rseitz01/fhgr-bachelorthesis-camera-calibration/doc/pres/single-led.jpg

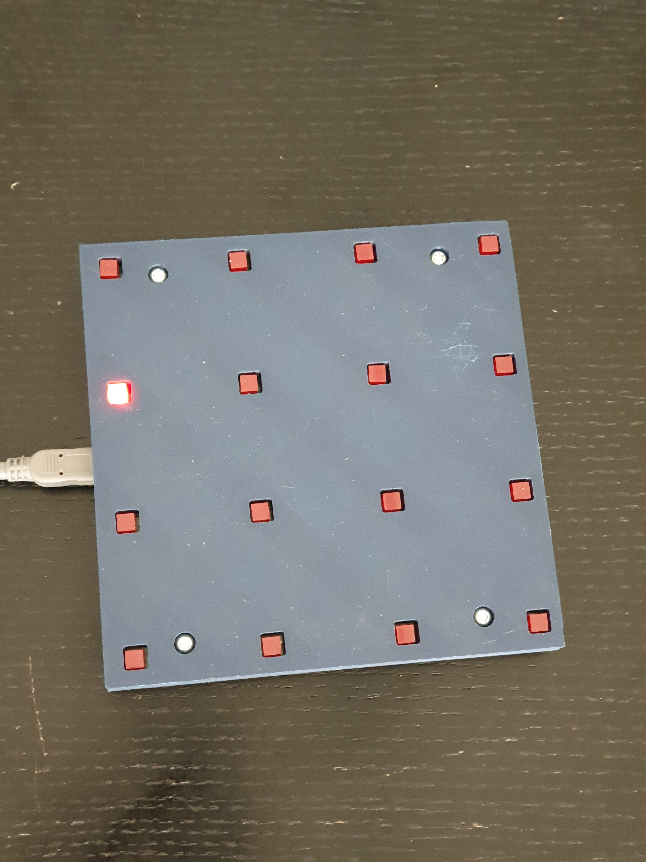
doc/pres/single-led.jpg
