rseitz01/fhgr-bachelorthesis-camera-calibration/doc/measurements/data_76097.bmp

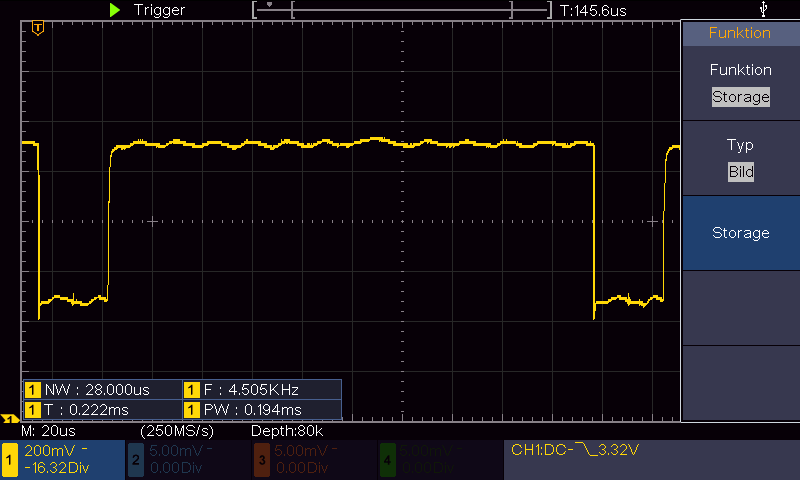
doc/measurements/data_76097.bmp
