rseitz01/fhgr-bachelorthesis-camera-calibration/doc/measurements/data_93169.bmp

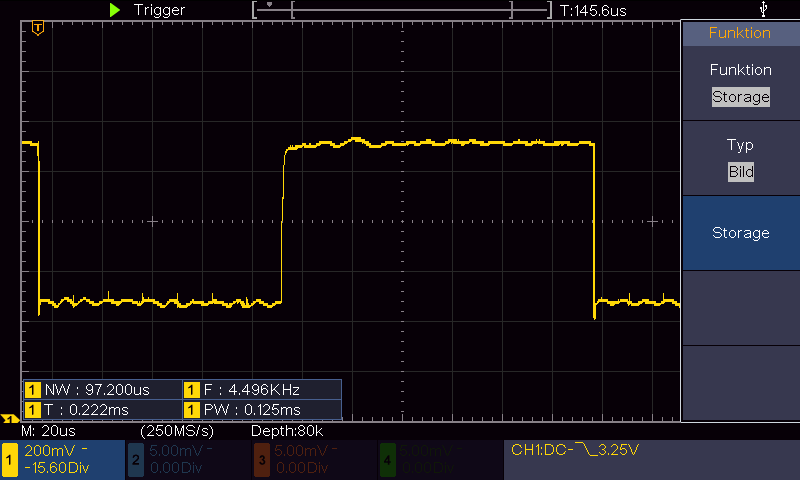
doc/measurements/data_93169.bmp
