rseitz01/fhgr-bachelorthesis-camera-calibration/doc/measurements/data_97243m.bmp

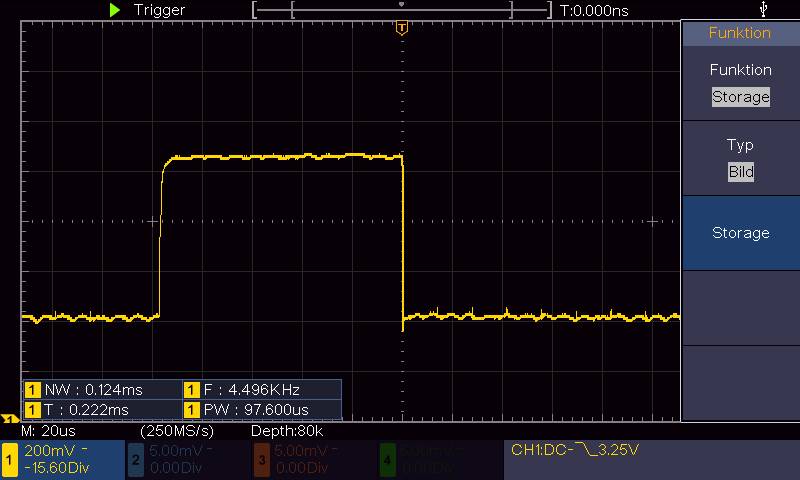
doc/measurements/data_97243m.bmp
