rseitz01/fhgr-bachelorthesis-camera-calibration/doc/measurements/data_104201.bmp

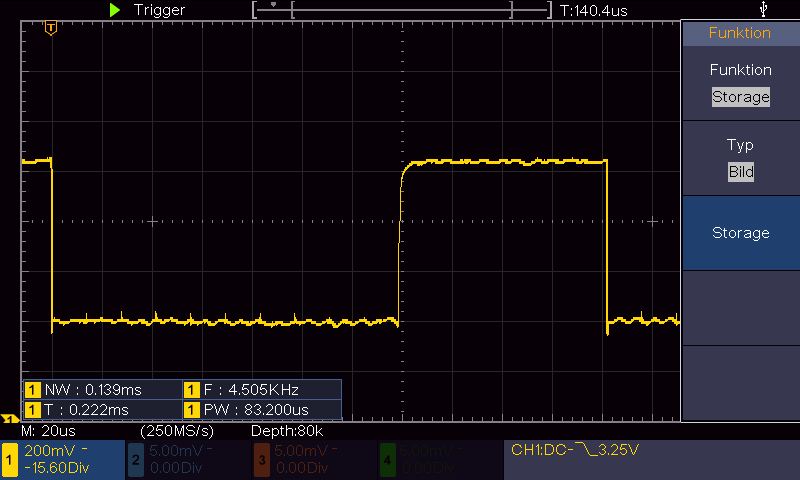
doc/measurements/data_104201.bmp
