rseitz01/fhgr-bachelorthesis-camera-calibration/doc/measurements/data_109735.bmp

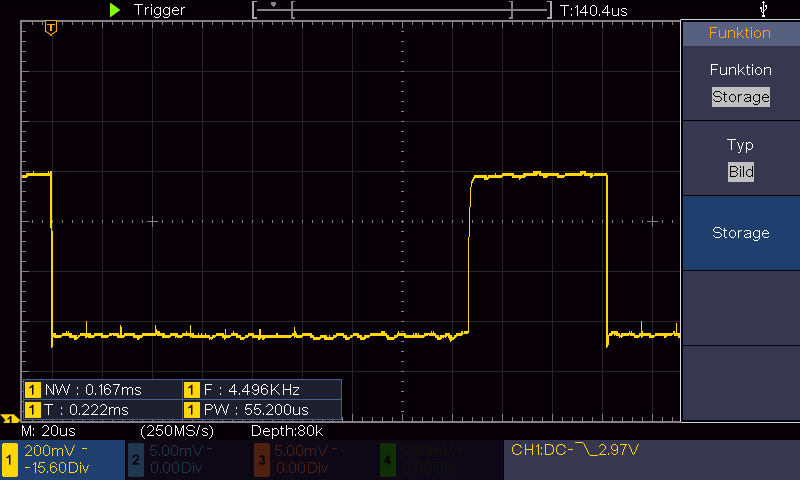
doc/measurements/data_109735.bmp
