rseitz01/fhgr-bachelorthesis-camera-calibration/doc/measurements/data_115571.bmp

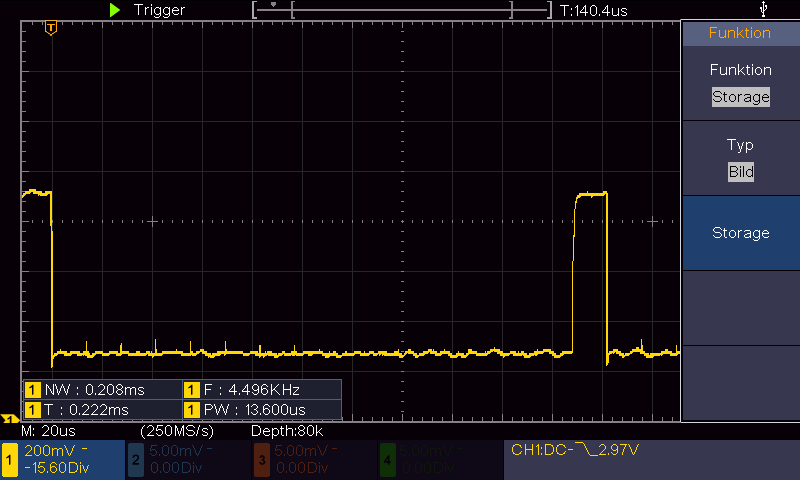
doc/measurements/data_115571.bmp
