rseitz01/fhgr-bachelorthesis-camera-calibration/doc/measurements/scope_19.png

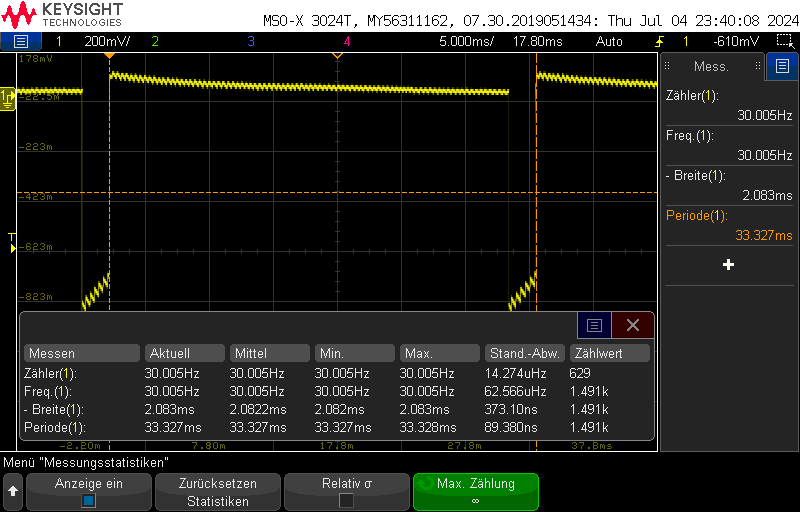
doc/measurements/scope_19.png
