rseitz01/fhgr-bachelorthesis-camera-calibration/doc/measurements/scope_20.png

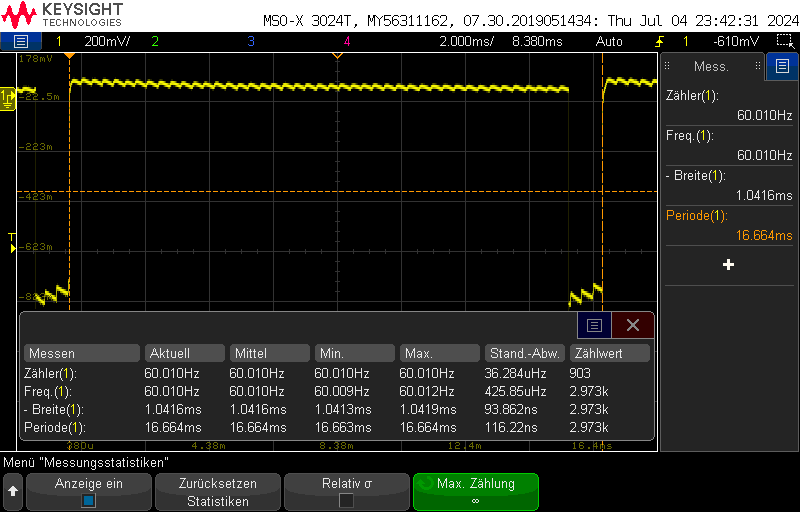
doc/measurements/scope_20.png
