rseitz01/fhgr-bachelorthesis-camera-calibration/doc/measurements/scope_21.bmp

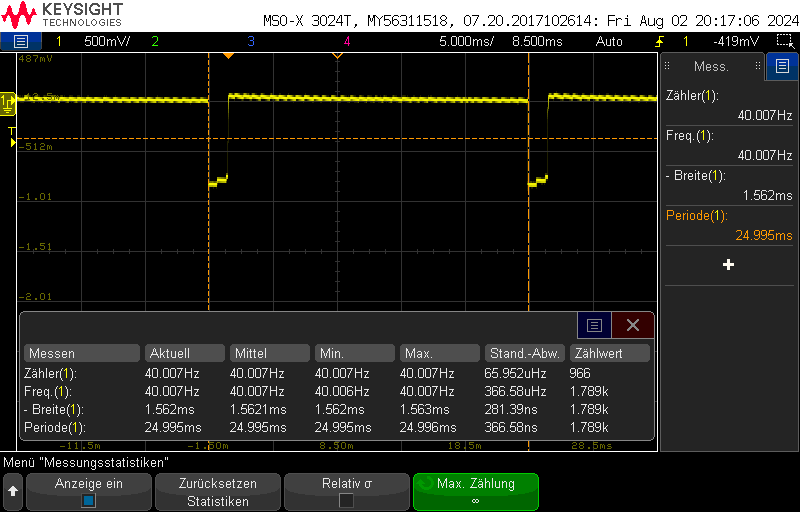
doc/measurements/scope_21.bmp
