rseitz01/fhgr-bachelorthesis-camera-calibration/doc/measurements/scope_27.bmp

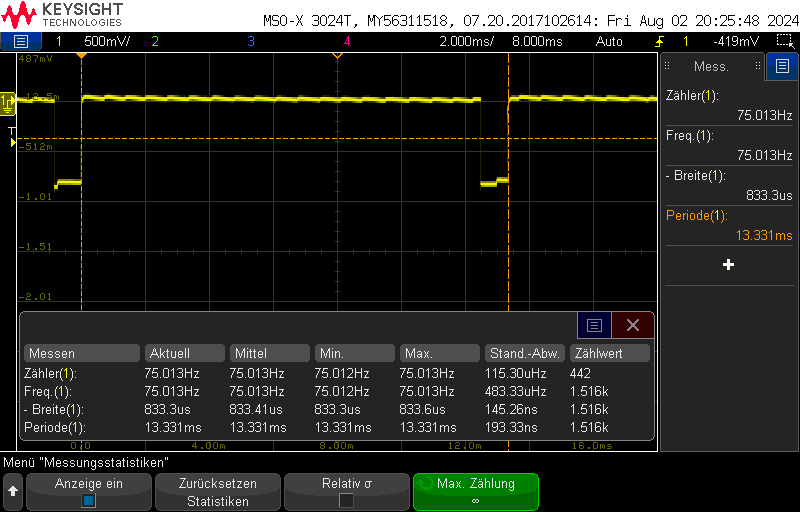
doc/measurements/scope_27.bmp
