rseitz01/fhgr-bachelorthesis-camera-calibration/doc/results/30fps-4999us-at-29-85fps-vs-both.png

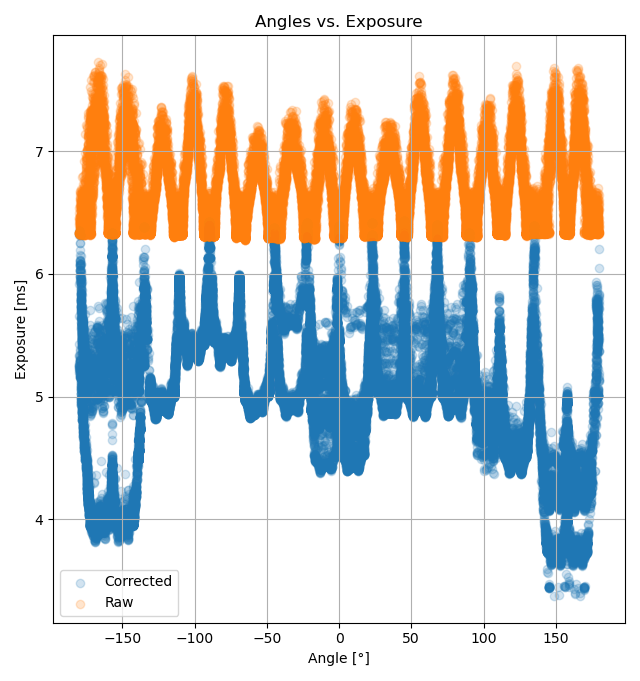
doc/results/30fps-4999us-at-29-85fps-vs-both.png
