rseitz01/fhgr-bachelorthesis-camera-calibration/doc/results/59-99fps-4999us-at-40-000000fps-exposure-both.png

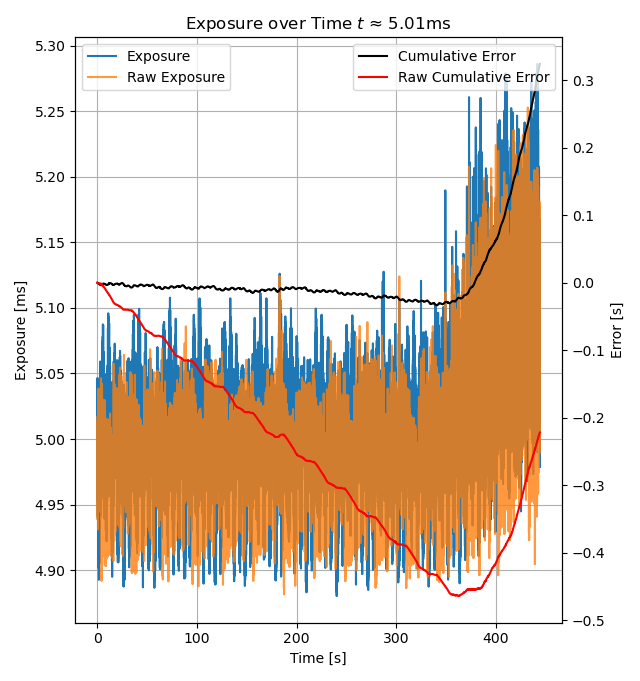
doc/results/59-99fps-4999us-at-40-000000fps-exposure-both.png
