rseitz01/fhgr-bachelorthesis-camera-calibration/doc/results/59-99fps-4999us-at-50-000000fps-fps-both.png

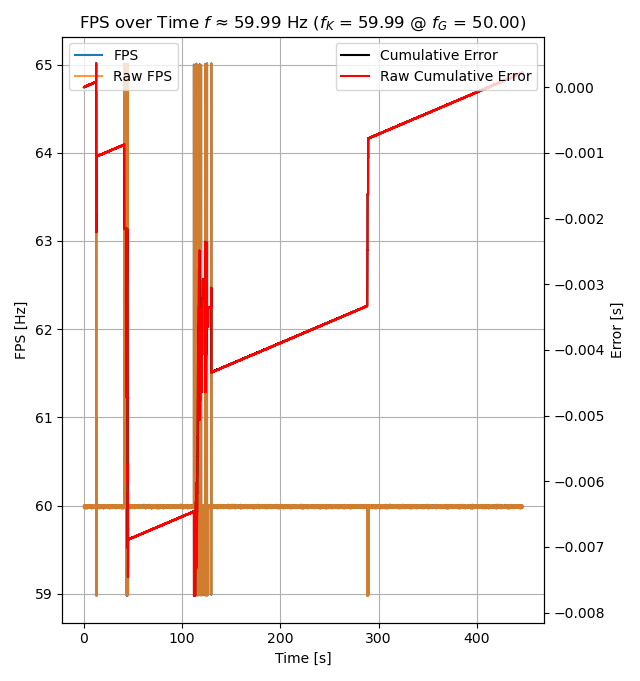
doc/results/59-99fps-4999us-at-50-000000fps-fps-both.png
