rseitz01/fhgr-bachelorthesis-camera-calibration/doc/results/59-99fps-4999us-at-56-250000fps-vs-both.png

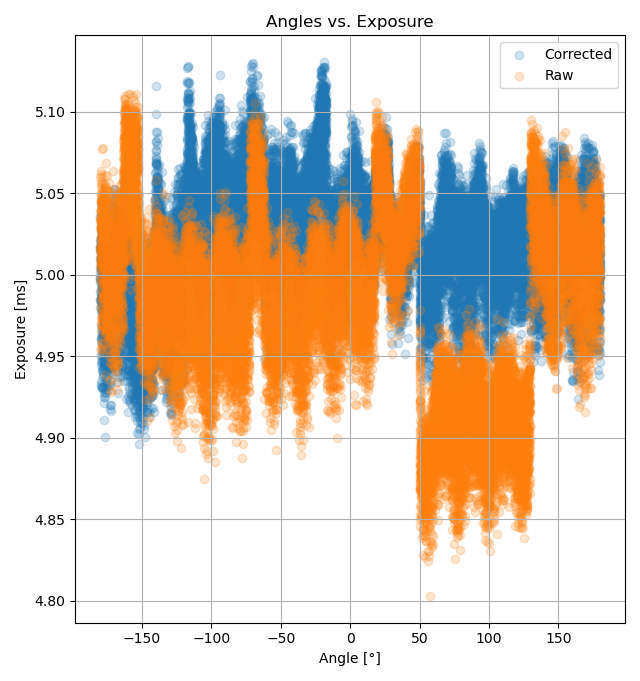
doc/results/59-99fps-4999us-at-56-250000fps-vs-both.png
