rseitz01/fhgr-bachelorthesis-camera-calibration/doc/results/59-99fps-4999us-at-64-285713fps-exposure.png

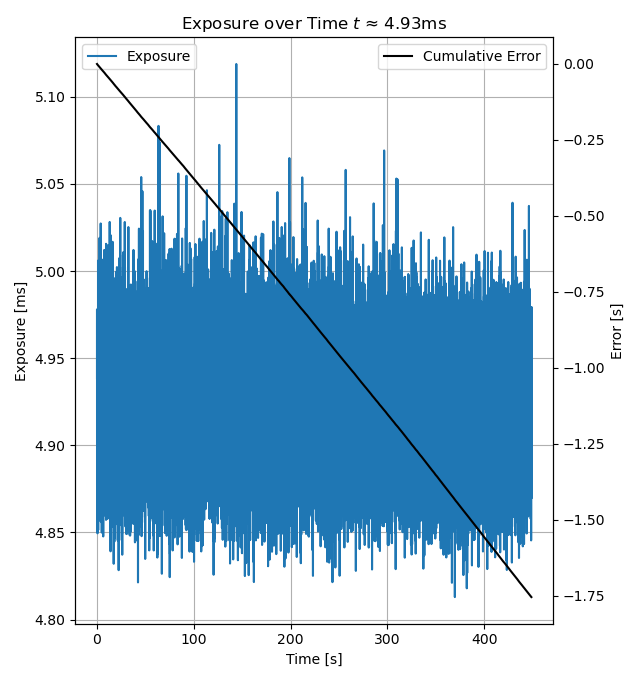
doc/results/59-99fps-4999us-at-64-285713fps-exposure.png
