rseitz01/fhgr-bachelorthesis-camera-calibration/doc/results/59-99fps-4999us-at-75-000000fps-fps.png

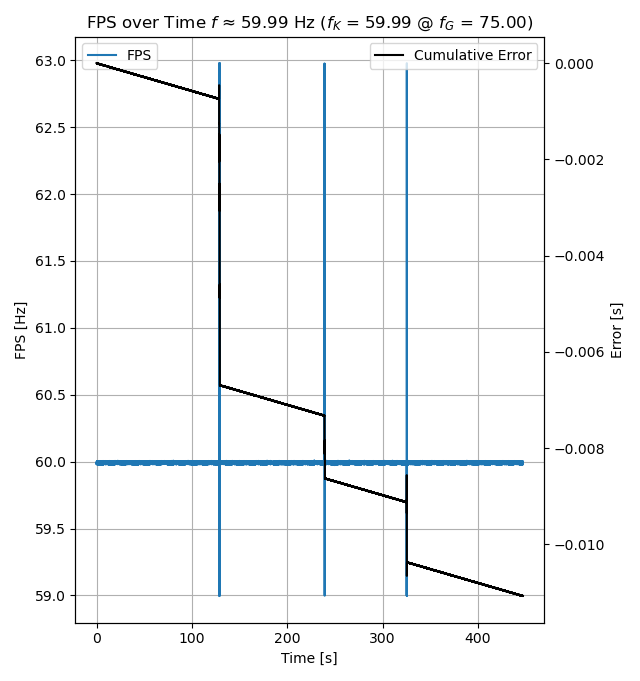
doc/results/59-99fps-4999us-at-75-000000fps-fps.png
