rseitz01/fhgr-bachelorthesis-camera-calibration/doc/results/59-99fps-4999us-at-120-000000fps-exposure.png

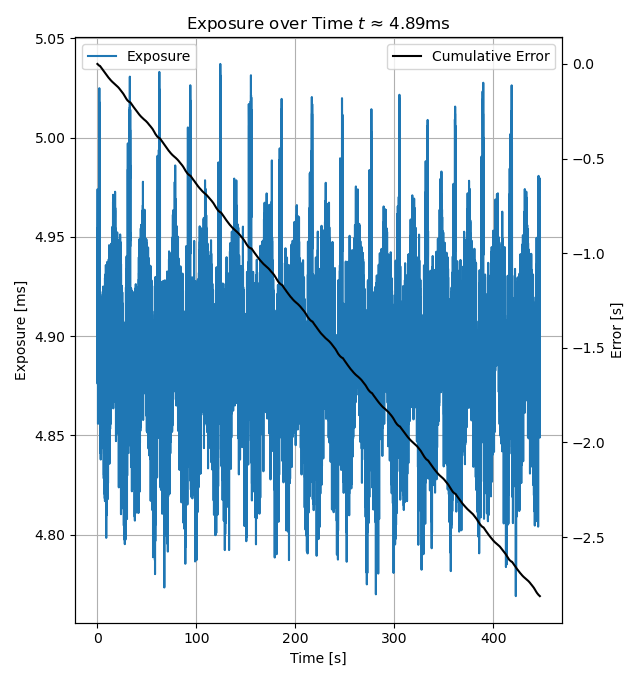
doc/results/59-99fps-4999us-at-120-000000fps-exposure.png
