rseitz01/fhgr-bachelorthesis-camera-calibration/doc/results/59.99fps-4999us-at-59.7fps-stats.png

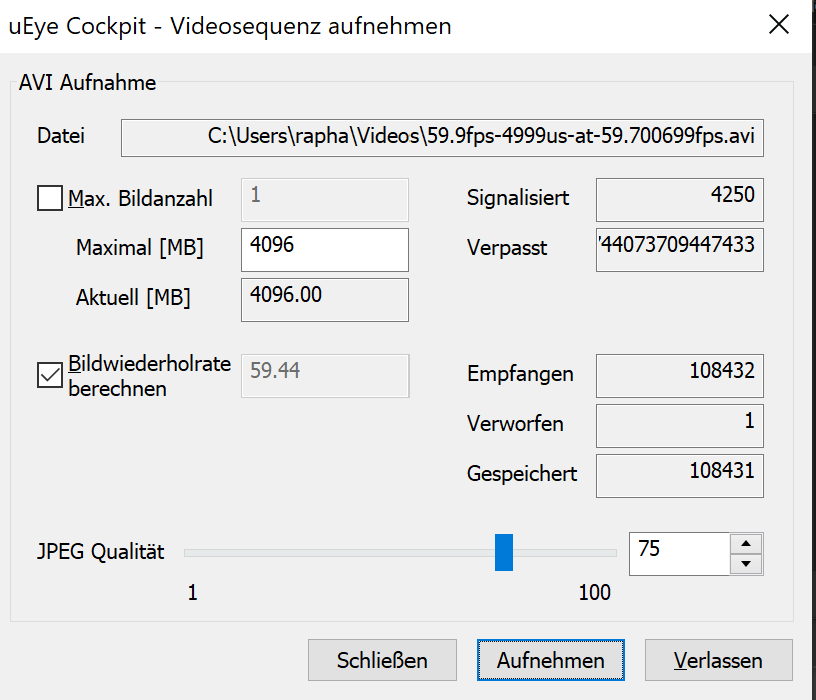
doc/results/59.99fps-4999us-at-59.7fps-stats.png
