rseitz01/fhgr-bachelorthesis-camera-calibration/doc/results/60fps-4999us-at-60fps-stats.png

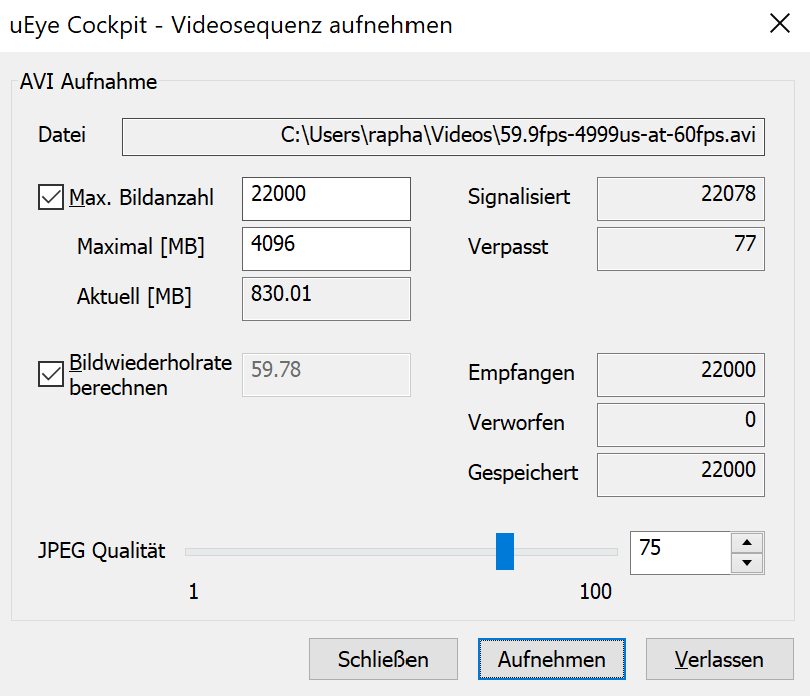
doc/results/60fps-4999us-at-60fps-stats.png
