rseitz01/fhgr-bachelorthesis-camera-calibration/doc/results/60fps-5000us-22k-exposure-both.png

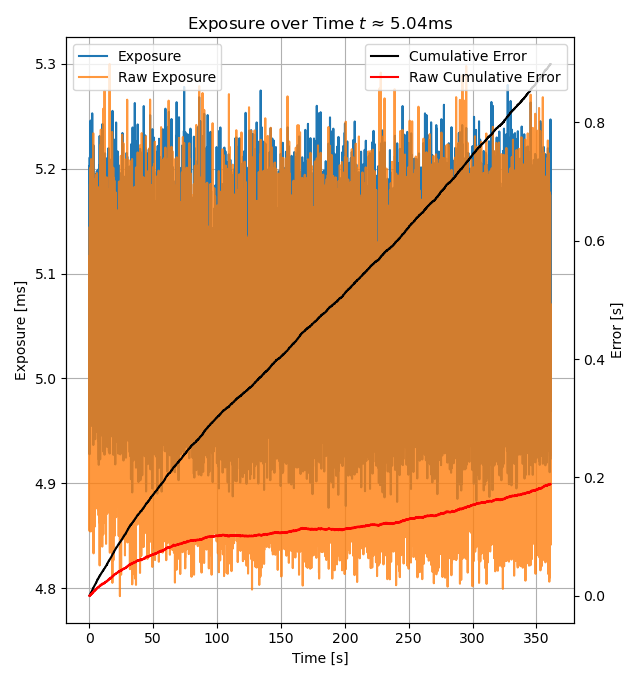
doc/results/60fps-5000us-22k-exposure-both.png
