rseitz01/fhgr-bachelorthesis-camera-calibration/doc/results/60fps-5000us-22k-fps.png

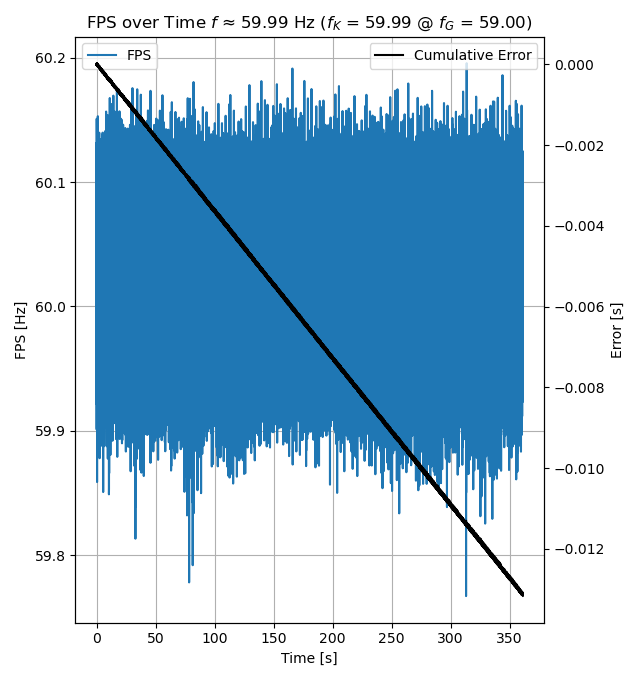
doc/results/60fps-5000us-22k-fps.png
