rseitz01/fhgr-bachelorthesis-camera-calibration/doc/results/60fps-5000us-22k-vs-both.png

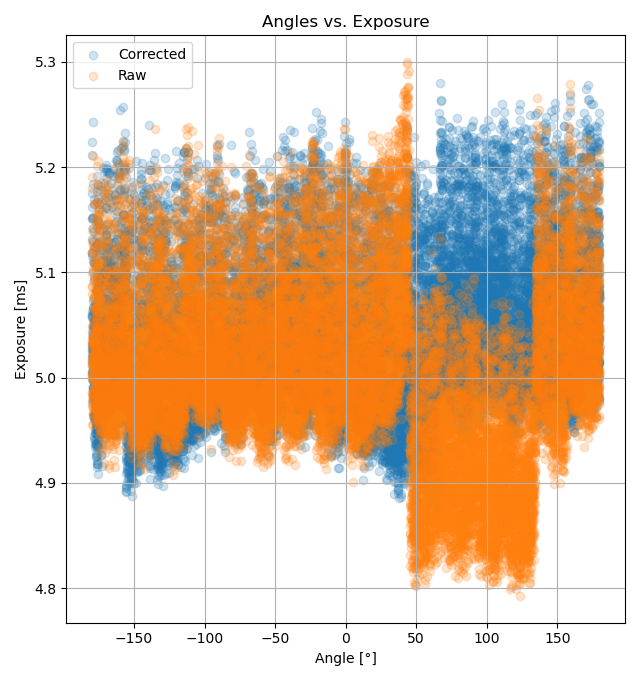
doc/results/60fps-5000us-22k-vs-both.png
