rseitz01/fhgr-bachelorthesis-camera-calibration/doc/results/60fps-at-59.700699fps-rolling-fps.png

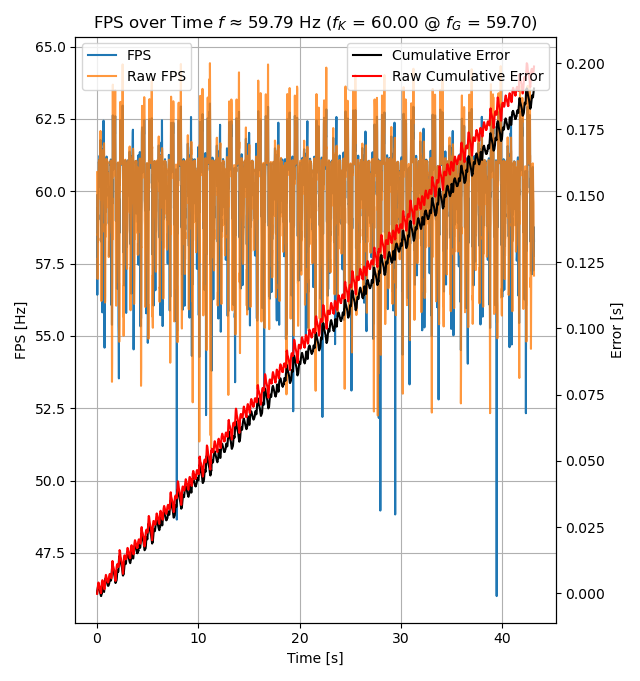
doc/results/60fps-at-59.700699fps-rolling-fps.png
