rseitz01/fhgr-bachelorthesis-camera-calibration/doc/results/60fps-at-59.700699fps-rolling-vs.png

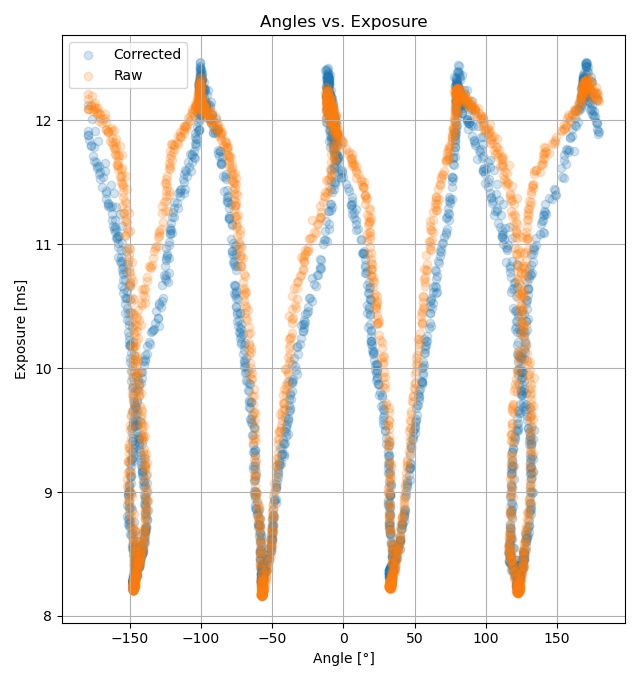
doc/results/60fps-at-59.700699fps-rolling-vs.png
