rseitz01/fhgr-bachelorthesis-camera-calibration/doc/results/285fps-2055us-22k_002-exposure-both.png

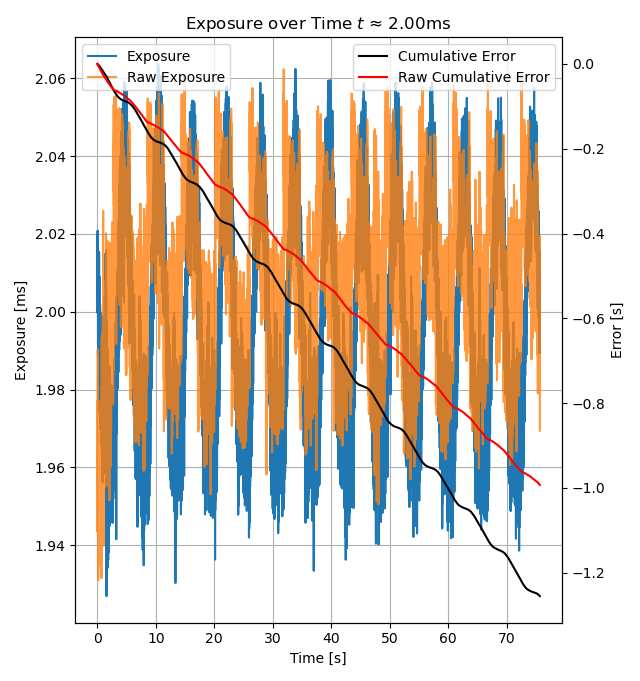
doc/results/285fps-2055us-22k_002-exposure-both.png
