rseitz01/fhgr-bachelorthesis-camera-calibration/doc/results/752fps-600us-85k-fps.png

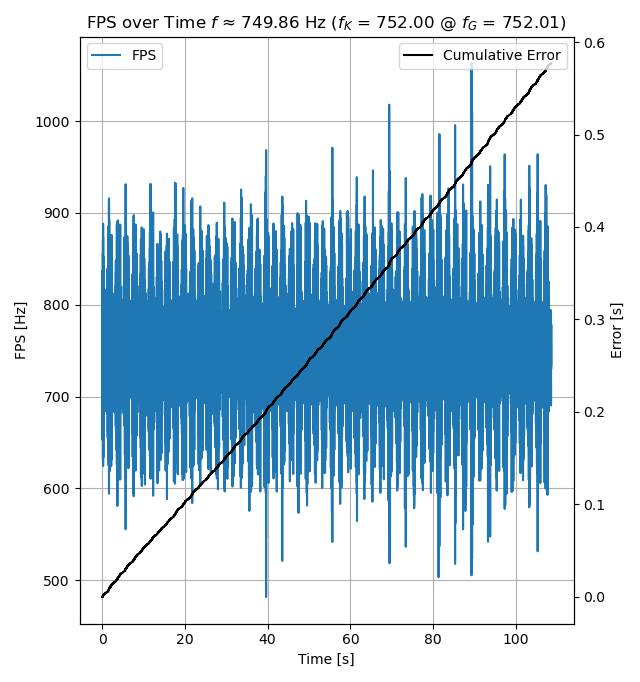
doc/results/752fps-600us-85k-fps.png
