rseitz01/fhgr-bachelorthesis-camera-calibration/doc/results/752fps-600us-85k-vs-both.png

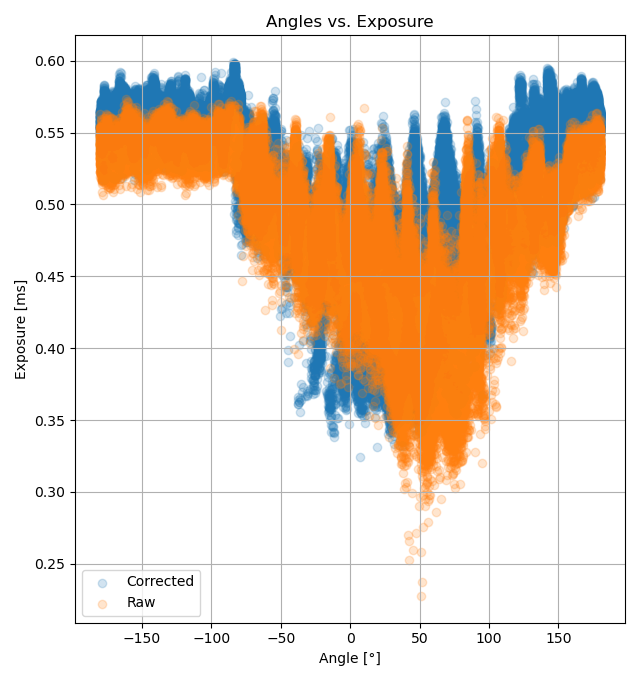
doc/results/752fps-600us-85k-vs-both.png
