rseitz01/fhgr-bachelorthesis-camera-calibration/src/camera-calibration/data/0400.png

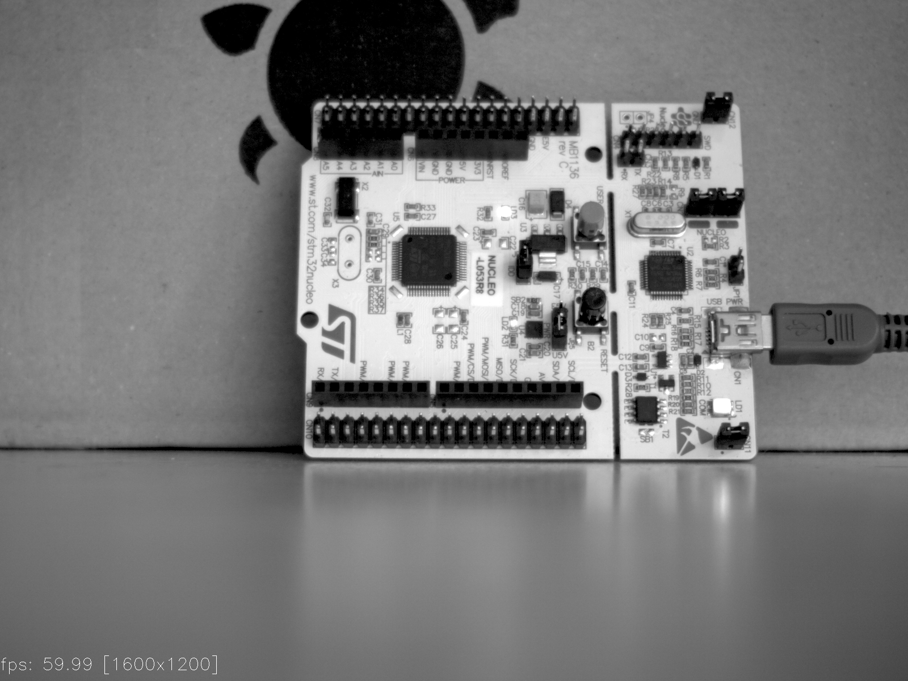
src/camera-calibration/data/0400.png
