rseitz01/fhgr-bachelorthesis-camera-calibration/src/camera-calibration/data/0900.png

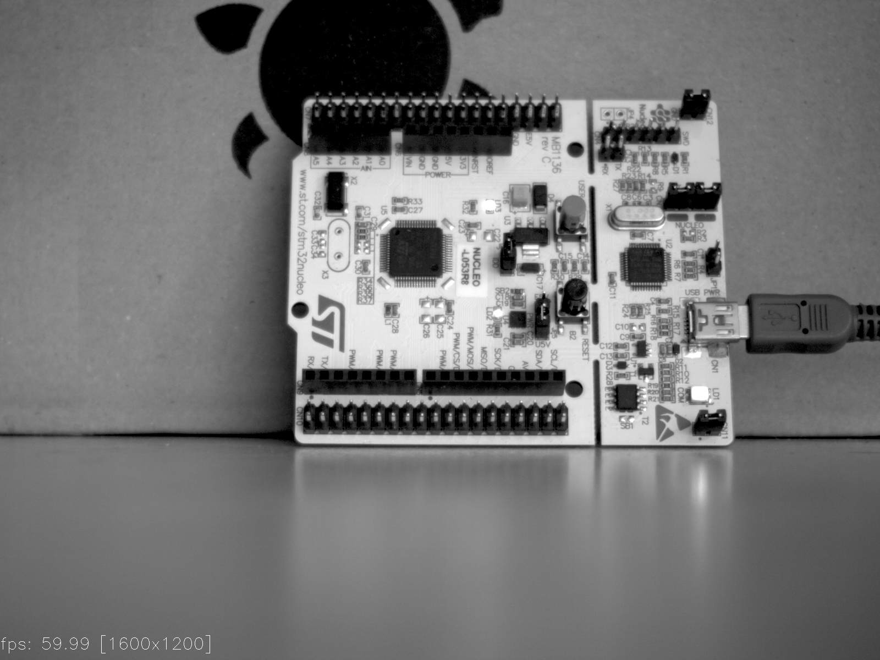
src/camera-calibration/data/0900.png
