rseitz01/fhgr-bachelorthesis-camera-calibration/src/camera-calibration/data_low_light/0000.png

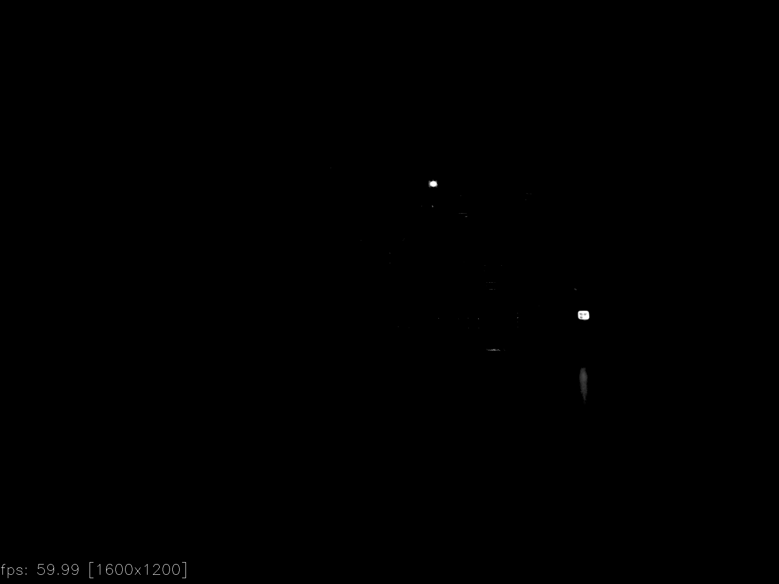
src/camera-calibration/data_low_light/0000.png
