rseitz01/fhgr-bachelorthesis-camera-calibration/ledrunner/sw-camera-calibration/Core/Src/main.c

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
/* Includes ------------------------------------------------------------------*/
#include "main.h"

/* USER CODE BEGIN Includes */
#include "str.h"
#include <stdio.h>
#include <string.h>
#include <errno.h>
#include <stdlib.h>
/* USER CODE END Includes */

/* USER CODE BEGIN PTD */

#define UART2_RXBUFFER_SIZE 	32

uint8_t UART2_RxBuffer[UART2_RXBUFFER_SIZE] = {0};
uint16_t UART2_RxBufferPos = 0;

/* USER CODE END PTD */

TIM_HandleTypeDef htim2;

UART_HandleTypeDef huart2;

/* USER CODE BEGIN PV */

#ifdef __GNUC__
#define PUTCHAR_PROTOTYPE int __io_putchar(int ch)
#else
#define PUTCHAR_PROTOTYPE int fputc(int ch, FILE *f)
#endif

PUTCHAR_PROTOTYPE
{
  HAL_UART_Transmit(&huart2, (uint8_t *)&ch, 1, HAL_MAX_DELAY);
  return ch;
}

/* USER CODE END PV */

void SystemClock_Config(void);
static void MX_GPIO_Init(void);
static void MX_USART2_UART_Init(void);
static void MX_TIM2_Init(void);
/**
  * @brief  The application entry point.
  * @retval int
  */
int main(void)
{
  /* MCU Configuration--------------------------------------------------------*/

  /* Reset of all peripherals, Initializes the Flash interface and the Systick. */
  HAL_Init();

  /* Configure the system clock */
  SystemClock_Config();

  /* Initialize all configured peripherals */
  MX_GPIO_Init();
  MX_USART2_UART_Init();
  MX_TIM2_Init();
  /* USER CODE BEGIN 2 */

  TIM2->CCR1 = 0;
  HAL_TIM_PWM_Start(&htim2, TIM_CHANNEL_1);
  HAL_UART_Receive_IT(&huart2, UART2_RxBuffer, 1); 	// somehow is required to start HAL_UART_RxCpltCallback

  char in[1024] = {0};
  uint16_t in_pos = 0;

  /* tlc enters normal mode on startup by default */
  HAL_GPIO_WritePin(TLC5926_LE_GPIO_Port, TLC5926_LE_Pin, GPIO_PIN_SET); /* high LE = transfer to latch */
  HAL_GPIO_WritePin(TLC5926_OE_GPIO_Port, TLC5926_OE_Pin, GPIO_PIN_RESET); /* low OE = drive LEDs */
  HAL_GPIO_WritePin(TLC5926_SDI_GPIO_Port, TLC5926_SDI_Pin, GPIO_PIN_SET);

  /* USER CODE END 2 */

  /* Infinite loop */
  /* USER CODE BEGIN WHILE */
  // TIM2->ARR = auto reload register
  // TIM2->PSC = prescaler
  //int base_MHZ_reciproc = 16667; // 1000; = 1kHz
  TIM2->PSC = 40; //(32)*base_MHZ_reciproc - 1; // 31(+1) => 1MHz counter
  TIM2->ARR = 813; //20;
  int state = 0;
  int led = 0;
  int latch = 0;

  HAL_TIM_Base_Start_IT(&htim2);

  while (1)
  {

	  if(UART2_RxBufferPos) {
		  size_t len = in_pos + UART2_RxBufferPos < 1024 ? UART2_RxBufferPos : 1024 - 1 - in_pos;
		  memcpy(in+in_pos, UART2_RxBuffer, len);
		  in_pos += UART2_RxBufferPos;
		  UART2_RxBufferPos = 0;
	  }

#if 0
	  if(memchr(in, '\n', 1024) || memchr(in, '\r', 1024)) {

		  if(!strncmp(in, "-help", strlen("-help"))) {
			  printf("HELP!\r\n");
		  }
		  if(!strncmp(in, "-pwm ", strlen("-pwm "))) {
			  char *in_num = in + strlen("-pwm ");
			  char *endptr = 0;
			  errno = 0;
			  long num = strtol(in_num, &endptr, 0);
			  if(errno || (!strchr("\n\r", *endptr)) || (num > TIM2->ARR)) {
				  printf("invalid input. enter integer from 0 to %li\r\n", TIM2->ARR);
			  } else {
				  TIM2->CCR1 = num;
			  }
		  }

		  /* at last, clear string */
		  memset(in, 0, 1024);
		  in_pos = 0;
	  }
#endif

#if 0
	  /* shift in a bunch of ones */
	  if (!state) {
		  if (led >= 700) {
			  HAL_GPIO_WritePin(TLC5926_SDI_GPIO_Port, TLC5926_SDI_Pin, 1);
			  led = 0;
		  } else {
			  HAL_GPIO_WritePin(TLC5926_SDI_GPIO_Port, TLC5926_SDI_Pin, 0);
		  }
		  ++led;
	  }
	  HAL_GPIO_WritePin(TLC5926_CLK_GPIO_Port, TLC5926_CLK_Pin, state);
	  state ^= 1;

	  //HAL_GPIO_WritePin(TLC5926_SDI_GPIO_Port, TLC5926_SDI_Pin, GPIO_PIN_RESET);
	  //HAL_GPIO_WritePin(TLC5926_CLK_GPIO_Port, TLC5926_CLK_Pin, GPIO_PIN_RESET);
#endif

    /* USER CODE END WHILE */

    /* USER CODE BEGIN 3 */
  }
  /* USER CODE END 3 */
}

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
/* USER CODE BEGIN 4 */

void HAL_UART_RxCpltCallback(UART_HandleTypeDef *huart)
{
	uint8_t c;
	HAL_UART_Receive_IT(&huart2, &c, 1);

	if(UART2_RxBufferPos < UART2_RXBUFFER_SIZE) {
		HAL_UART_Transmit(&huart2, &c, 1, 10);
		UART2_RxBuffer[UART2_RxBufferPos++] = c;
		switch(c) {
		case '\r': case '\n': {
			uint8_t response[] = "\r\n";
			HAL_UART_Transmit(&huart2, response, sizeof(response), 10);
		} break;
		case 8: { // backspace
			uint8_t response[] = " \b";
			HAL_UART_Transmit(&huart2, response, sizeof(response), 10);
		} break;
		}
	}
}


/* USER CODE END 4 */
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
